Graziellah/Electronique-bagdeuse/pico/spi/spi_3.png

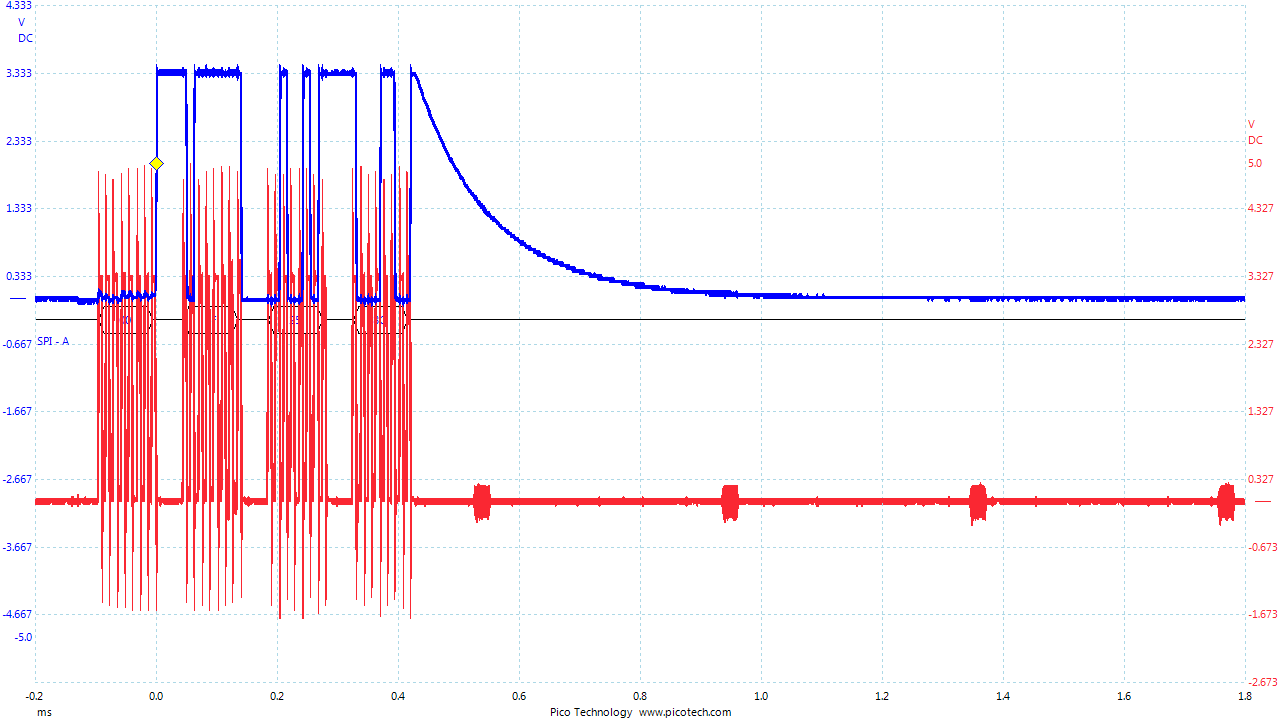
pico/spi/spi_3.png
