Graziellah/Electronique-bagdeuse/tps/42Electrons-TP02-REMAKE/TP02Remake/Project Outputs for TP02Remake/Job1.PDF

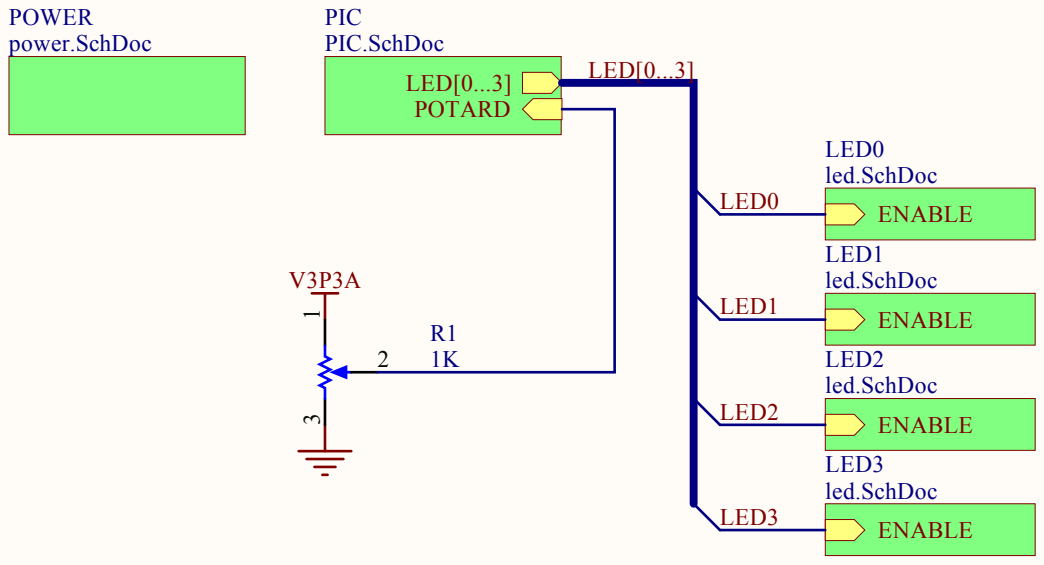
[picture p6: page 1]

Size: | N umber: | Rev
Date: / T ime: : 7 PM | | Sheet f *

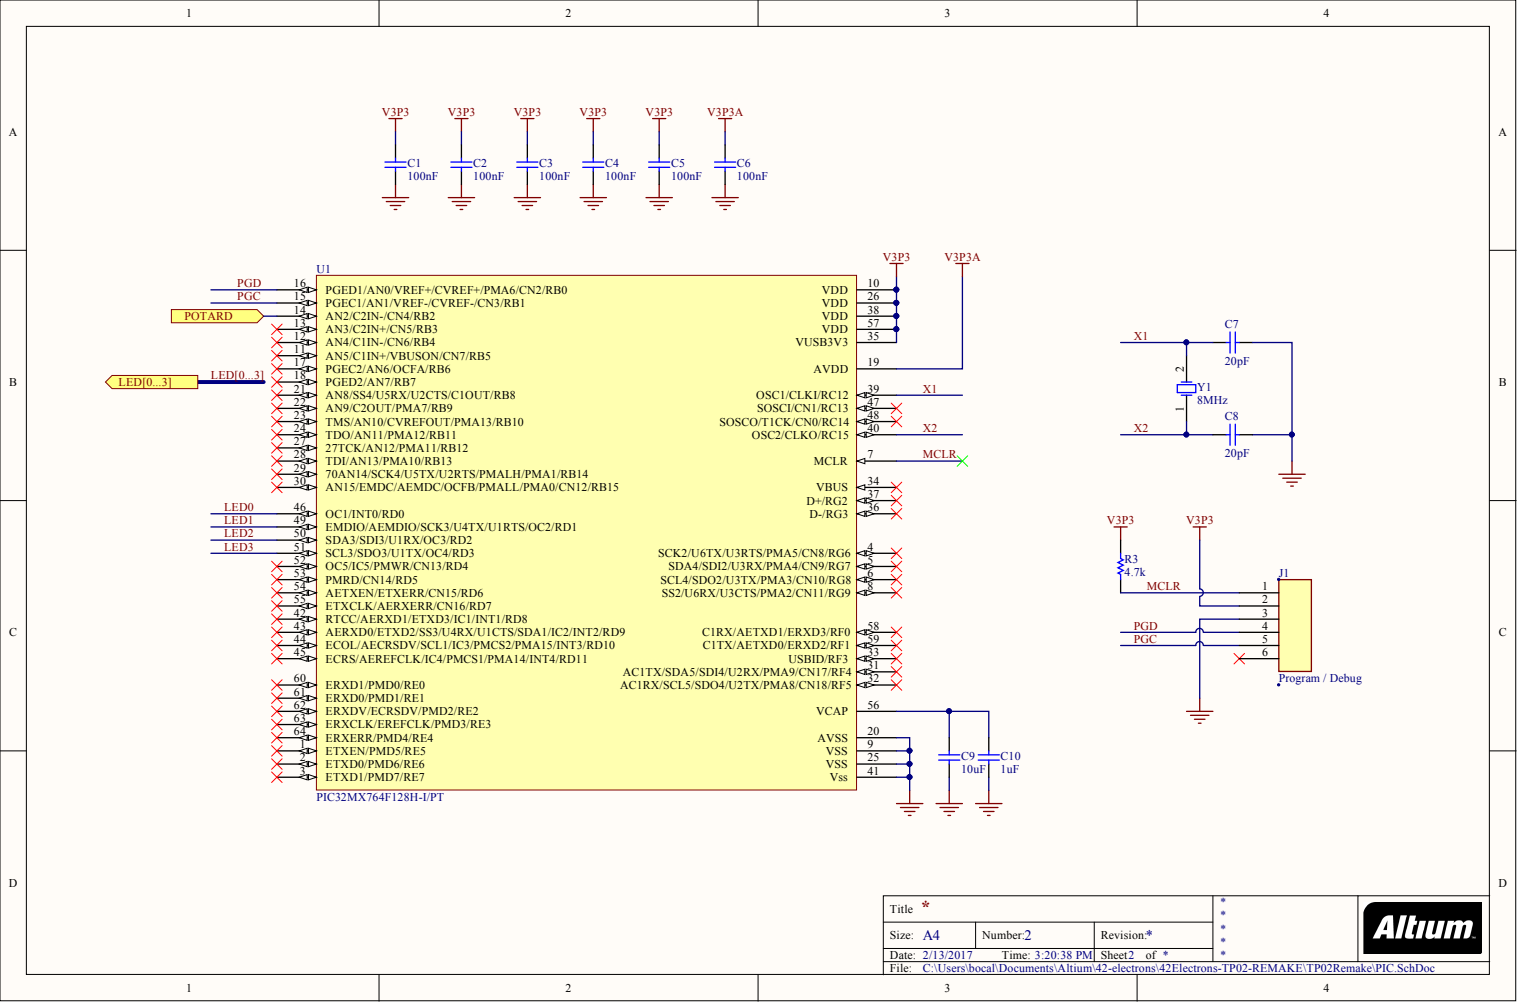
[picture p7: page 2]

2 0

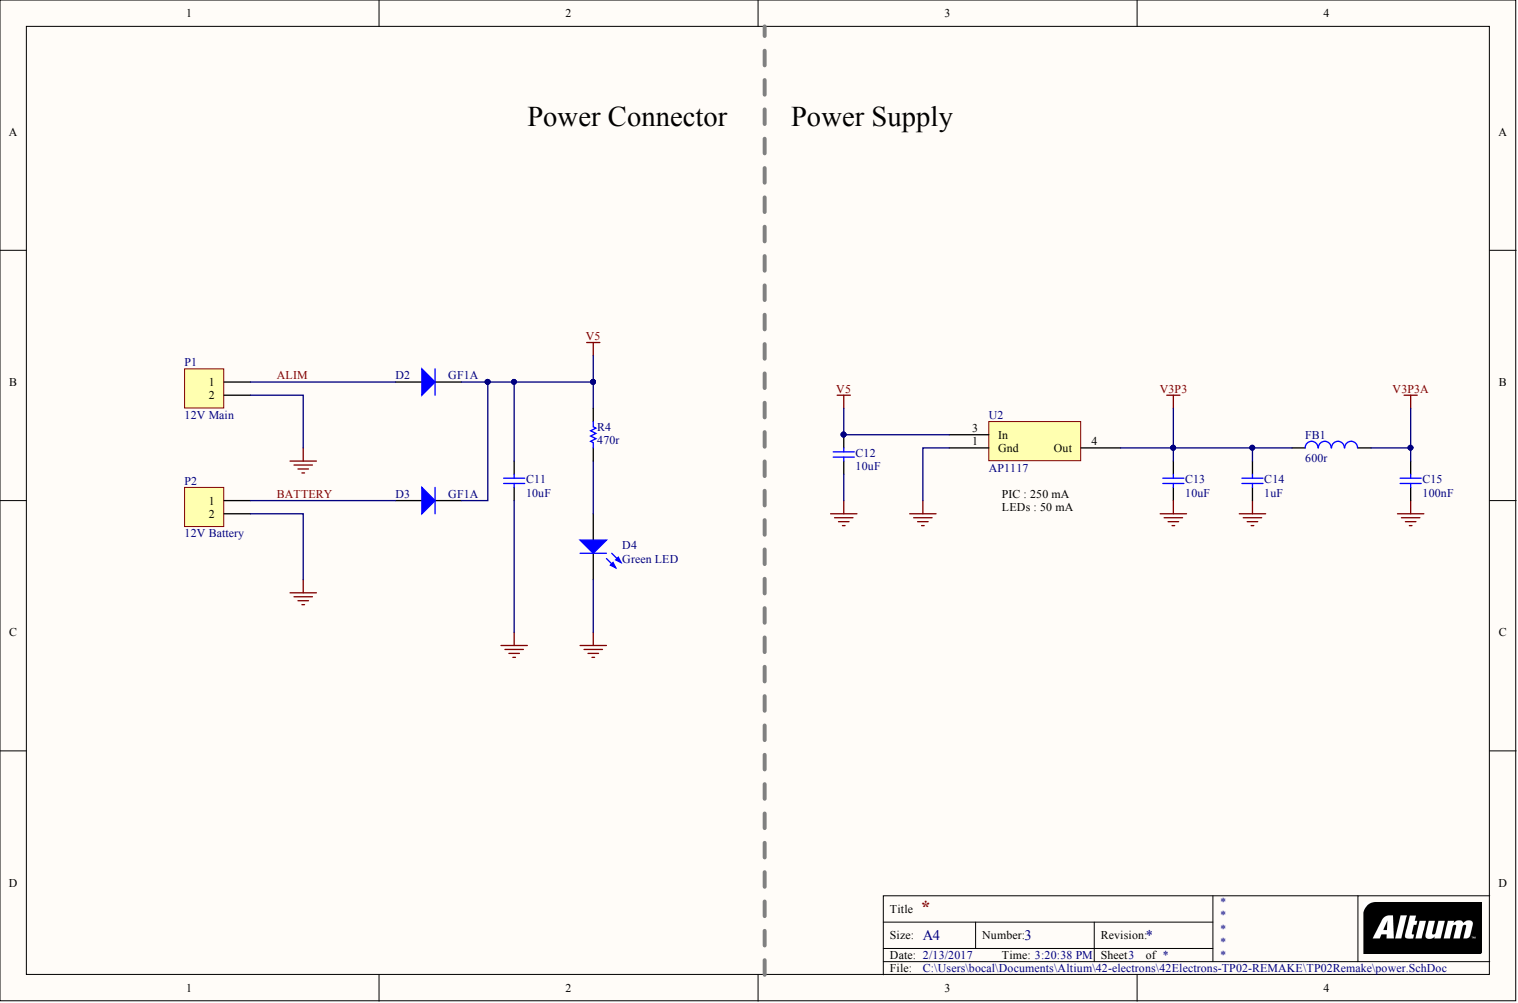
[picture p8: page 3]

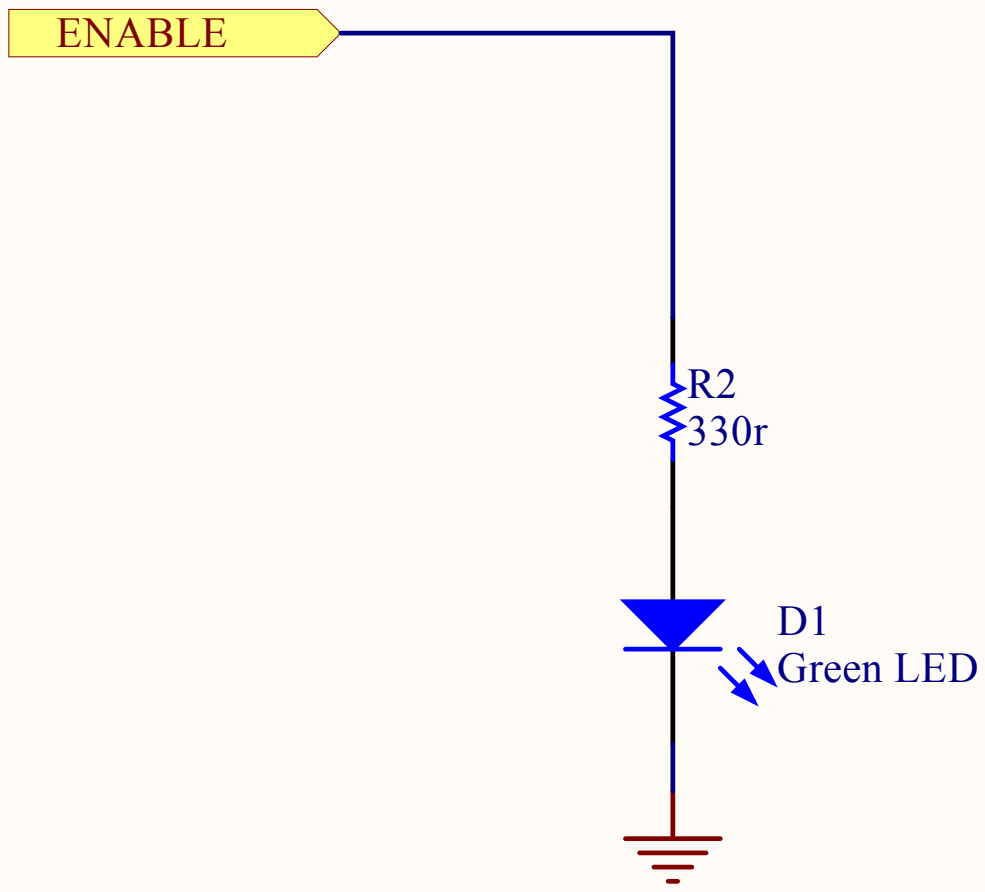
[picture p9: page 4]

Title * | * * *

Size: A4 | Number: 4 | Revision: *
2/13/2017 Time: 3:20:38 PM | | Sheet of *

C:\Users\bocal\Documents\Altium\42-electrons\42Electrons-TP02-REMAKE\TP02Remake\led.SchDoc
