Graziellah/Electronique-bagdeuse/tps/42Electrons-TP03/TP03/Project Outputs for TP02Remake/Assembly Drawings/Assembly Drawings.PDF

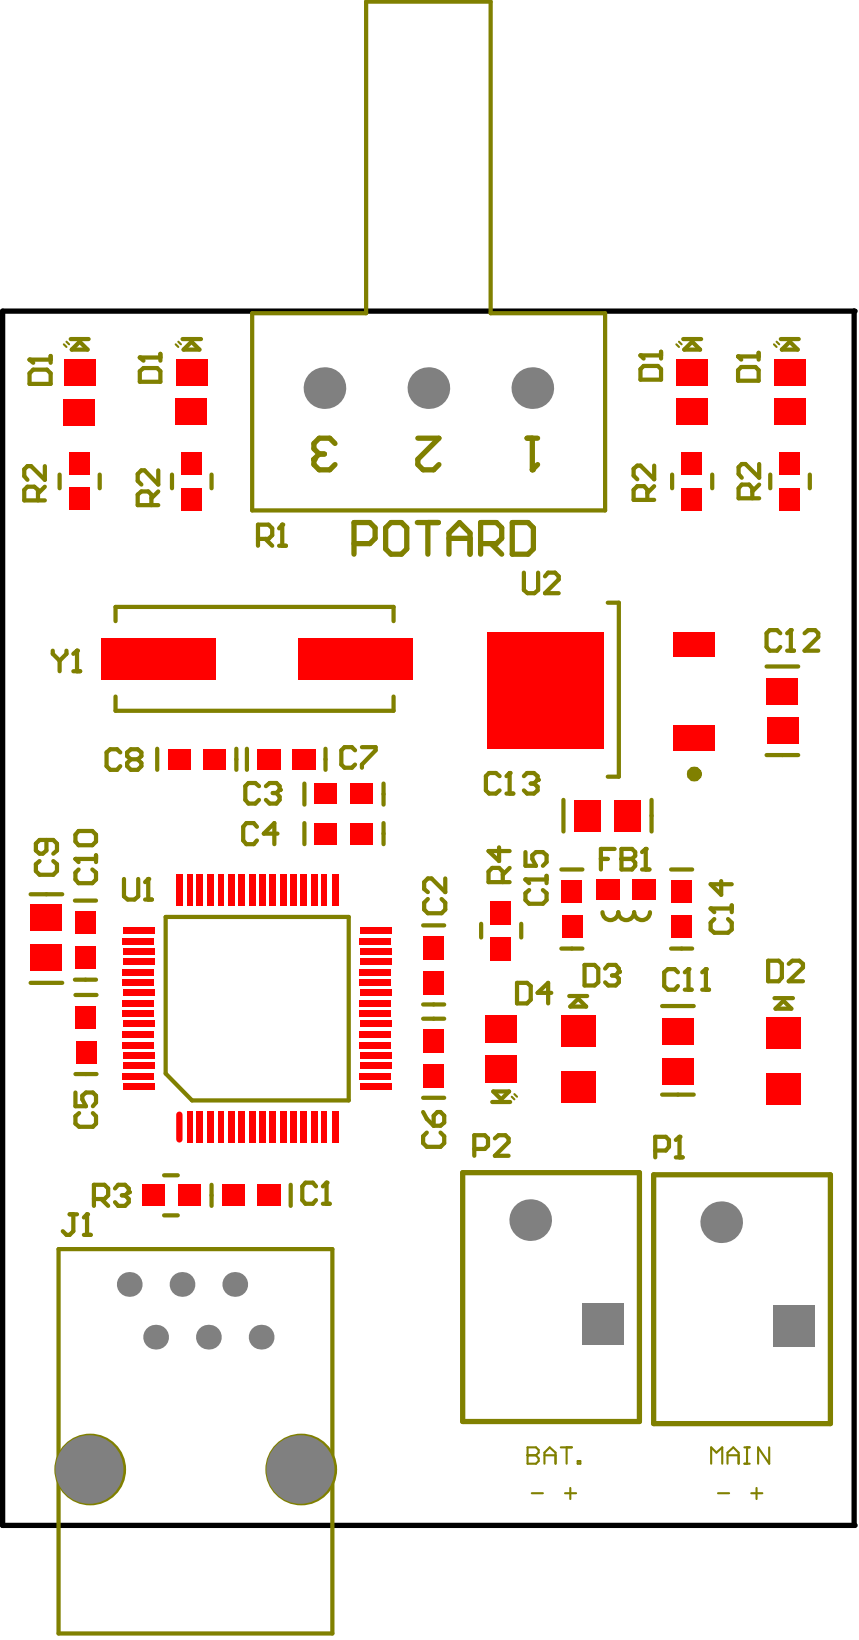
[picture p20: page 1]
