Graziellah/Electronique-bagdeuse/tps/42Electrons-TP03/TP03/Project Outputs for TP02Remake/Mechanical Drawings/Mechanical Drawings.PDF

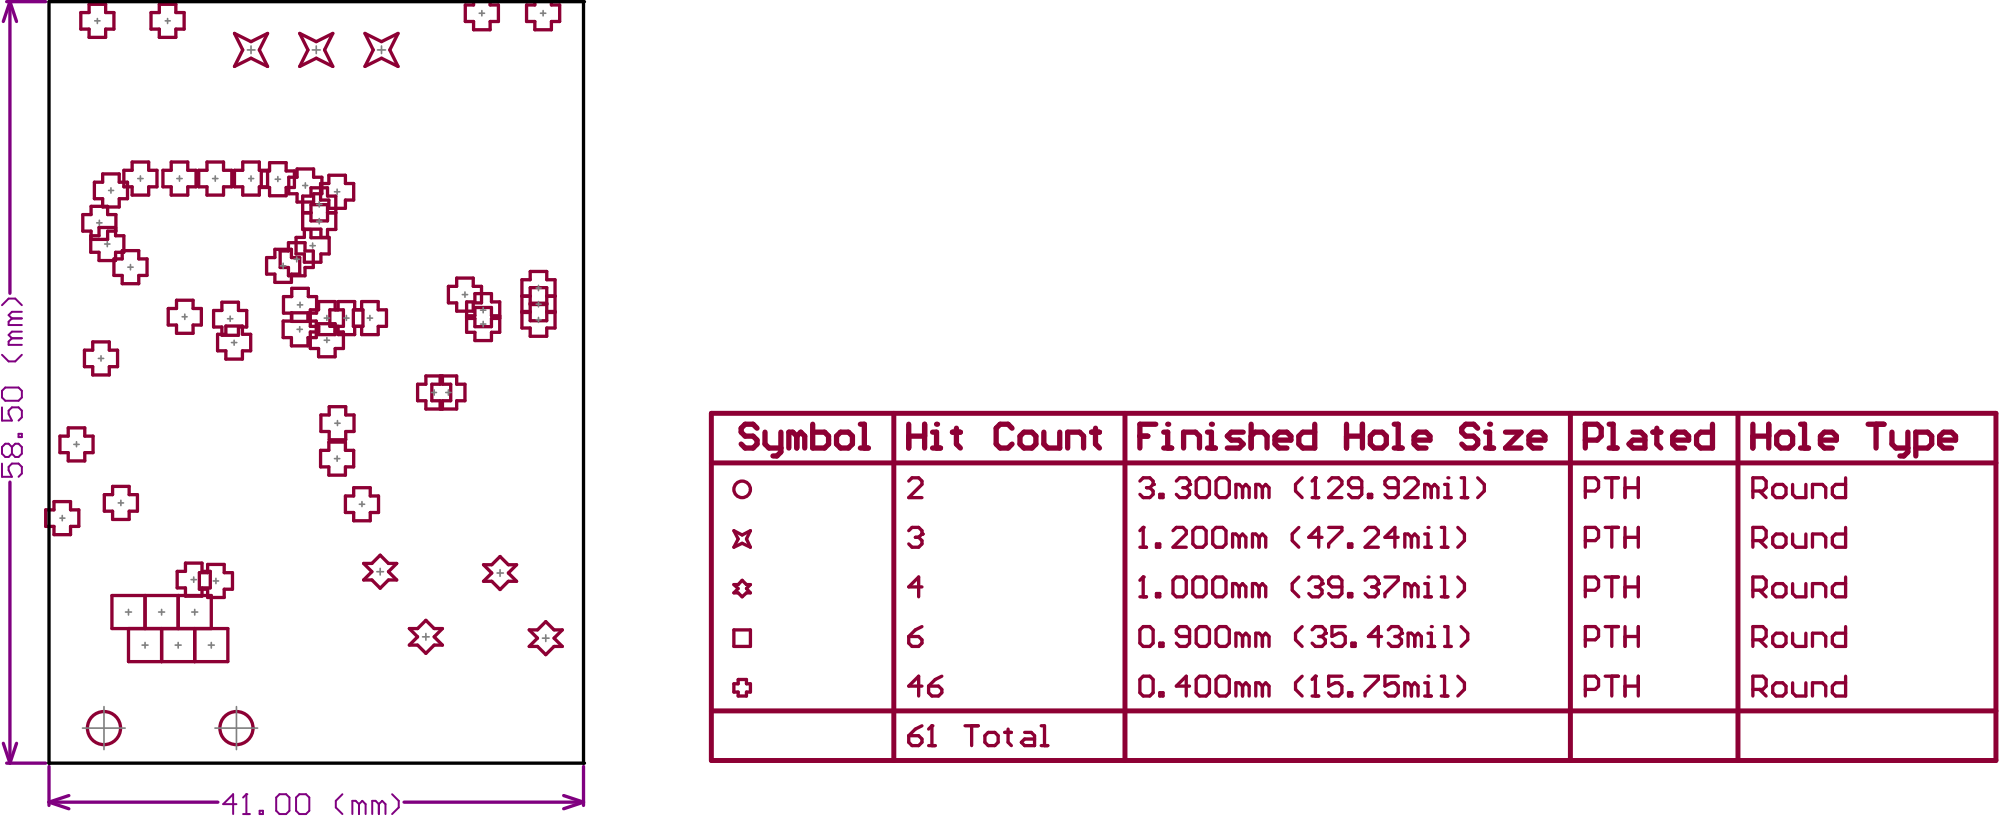
[picture p21: page 1]
