Graziellah/Electronique-bagdeuse/tps/42Electrons-TP03/TP03/Project Outputs for TP02Remake/Schematic Prints/Schematic Prints.PDF

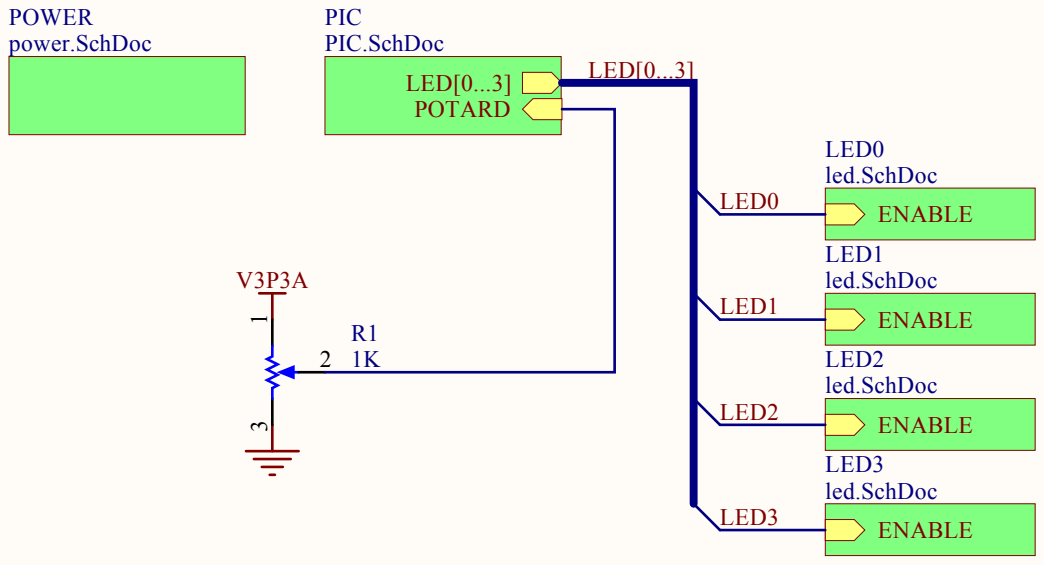
[picture p22: page 1]

Title * | * *

Size: A4 | Number: 1 | Revision: *
Date: 3/20/2017 Time: 1:25:23 PM | | Sheet of *

C:\Users\bocal\Documents\Altium\42-electrons\tps\42Electrons-TP03\TP03\TP2.SchDoc

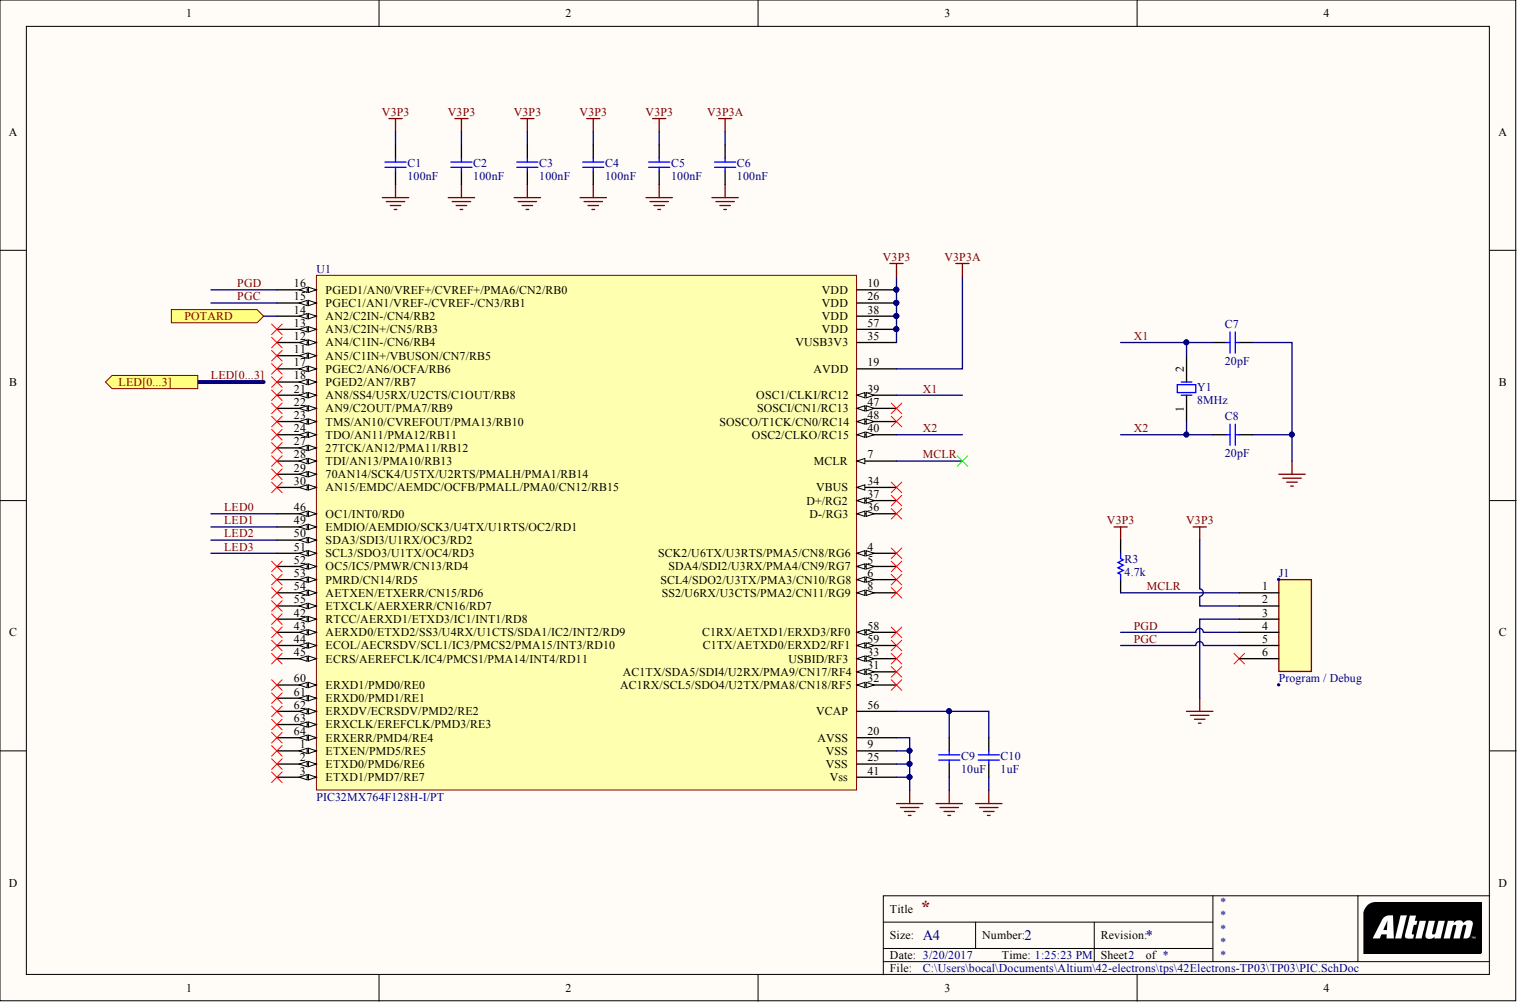
[picture p23: page 2]

2 0

Size: A | N umber: | Rev i s i o n :

/ / T ime: : : 3 PM | | Sheet o f

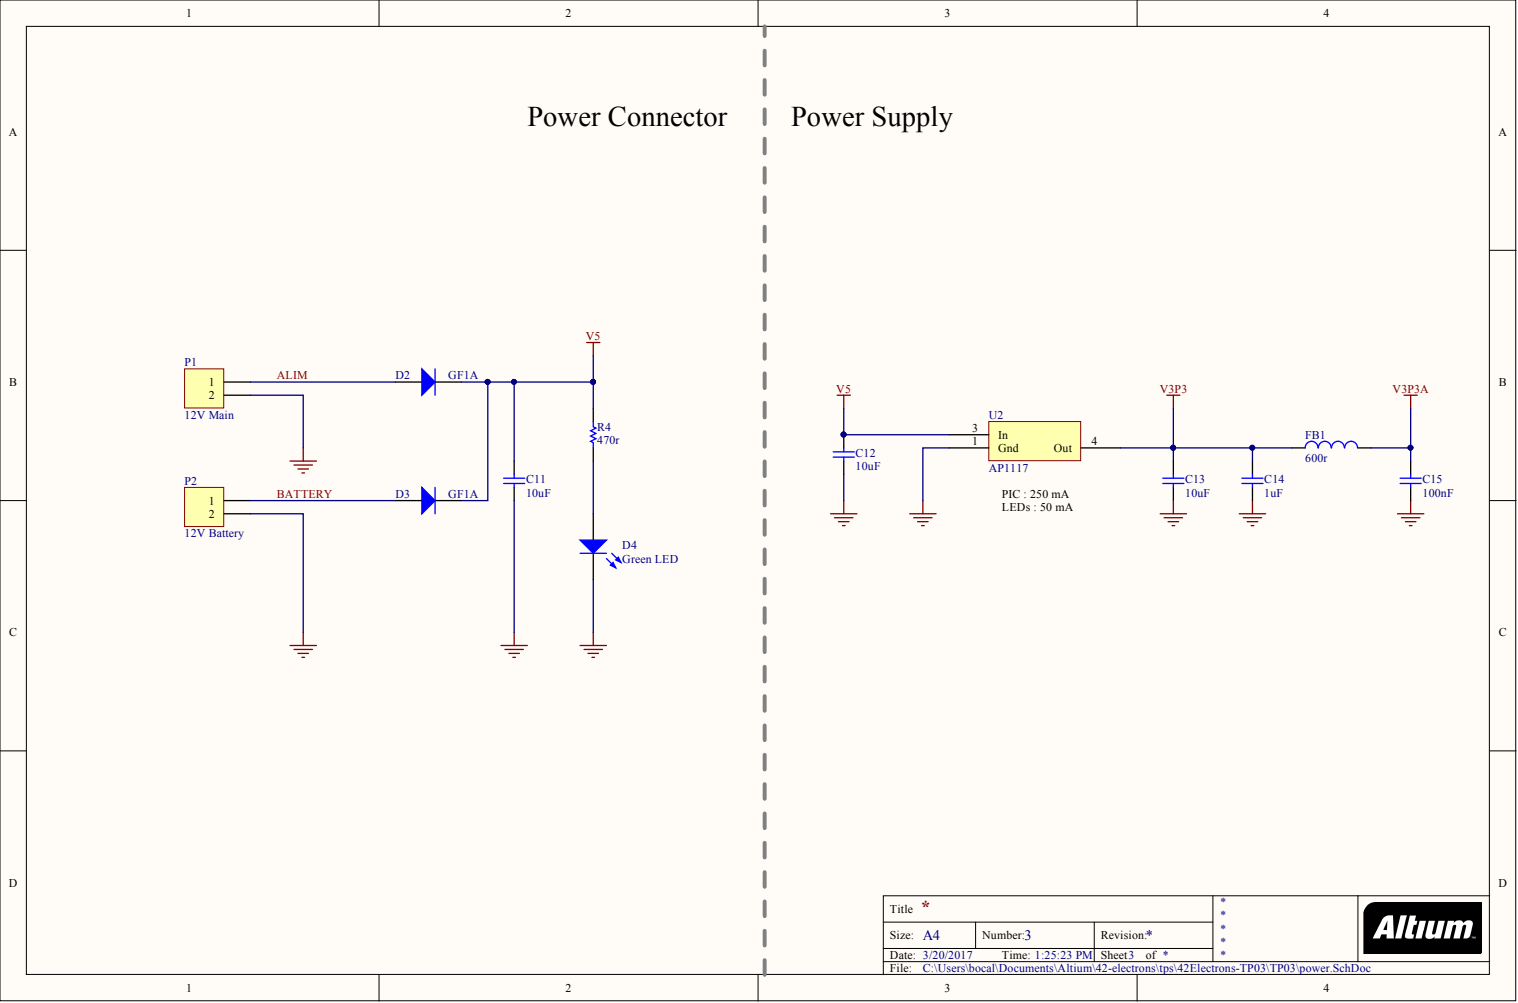
[picture p24: page 3]

Size: A | N umber: | Rev i s i o n :

/ / T ime: : : 3 PM | | Sheet o f

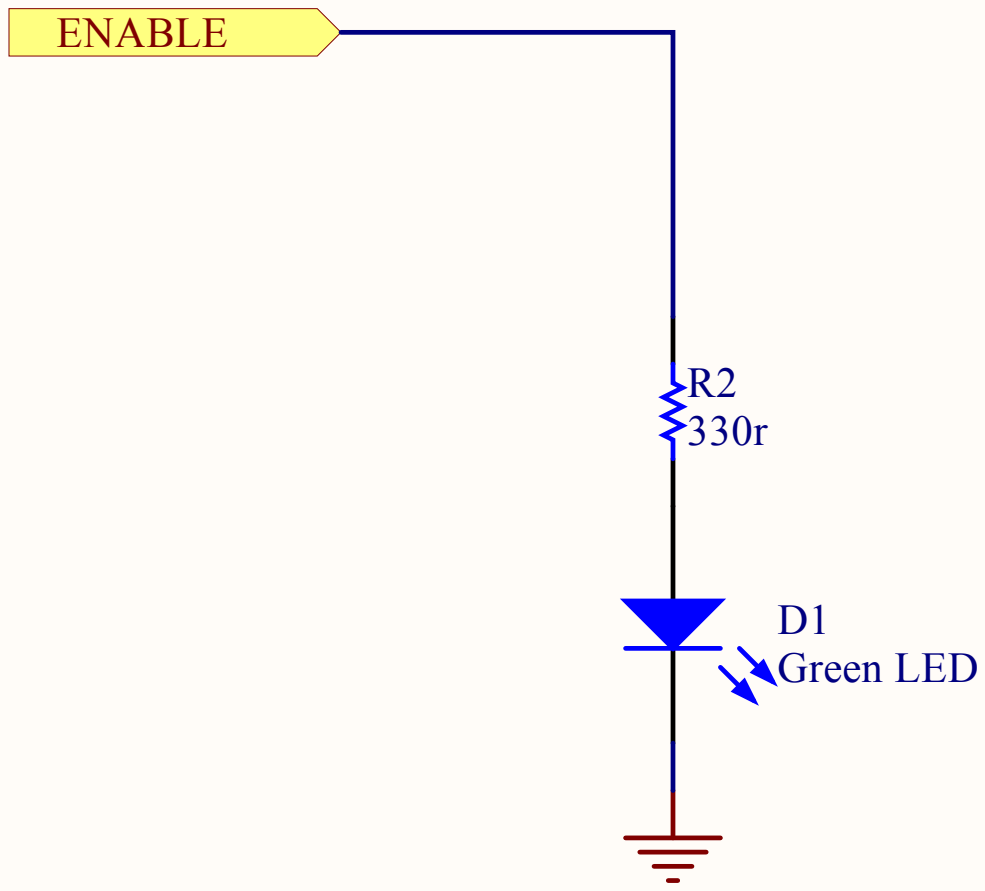
[picture p25: page 4]

Title * | * * *

Size: A4 | Number: 4 | Revision: *
3/20/2017 Time: 1:25:23 PM | | Sheet of *

C:\Users\bocal\Documents\Altium\42-electrons\tps\42Electrons-TP03\TP03\led.SchDoc
