Graziellah/Electronique-bagdeuse/tps/42Electrons-TP01-REMAKE/TP01Remake/Project Outputs for TP01Remake/Job1.PDF

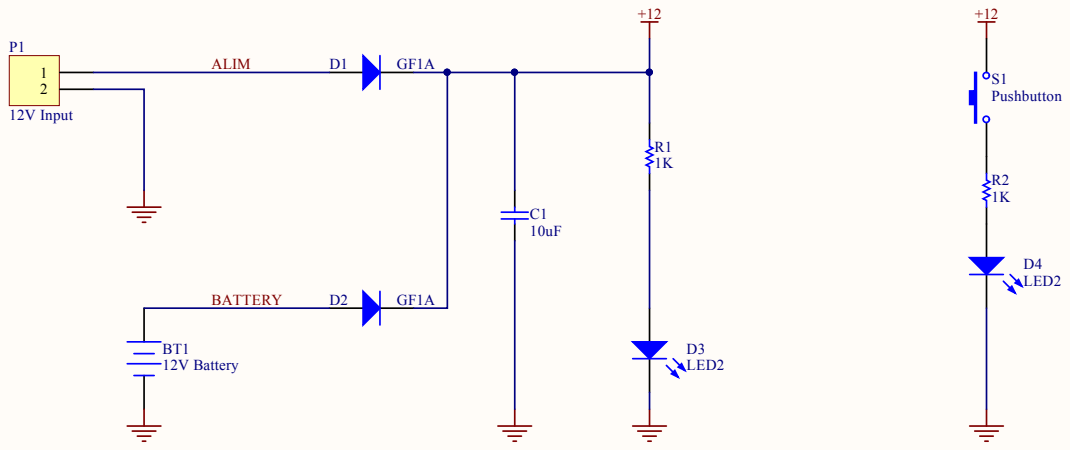
[picture p26: page 1]

Size: A 4 | N umber: 1 | Rev i s i o n : *
Date: 2 / 1 3 / 2 0 1 7 T ime: 2 : 5 6 : 0 6 PM | | Sheet * o f *
