Graziellah/Electronique-bagdeuse/tps/42Electrons-TP01-REMAKE/TP01Remake/Project Outputs for TP01Remake/Job2.PDF

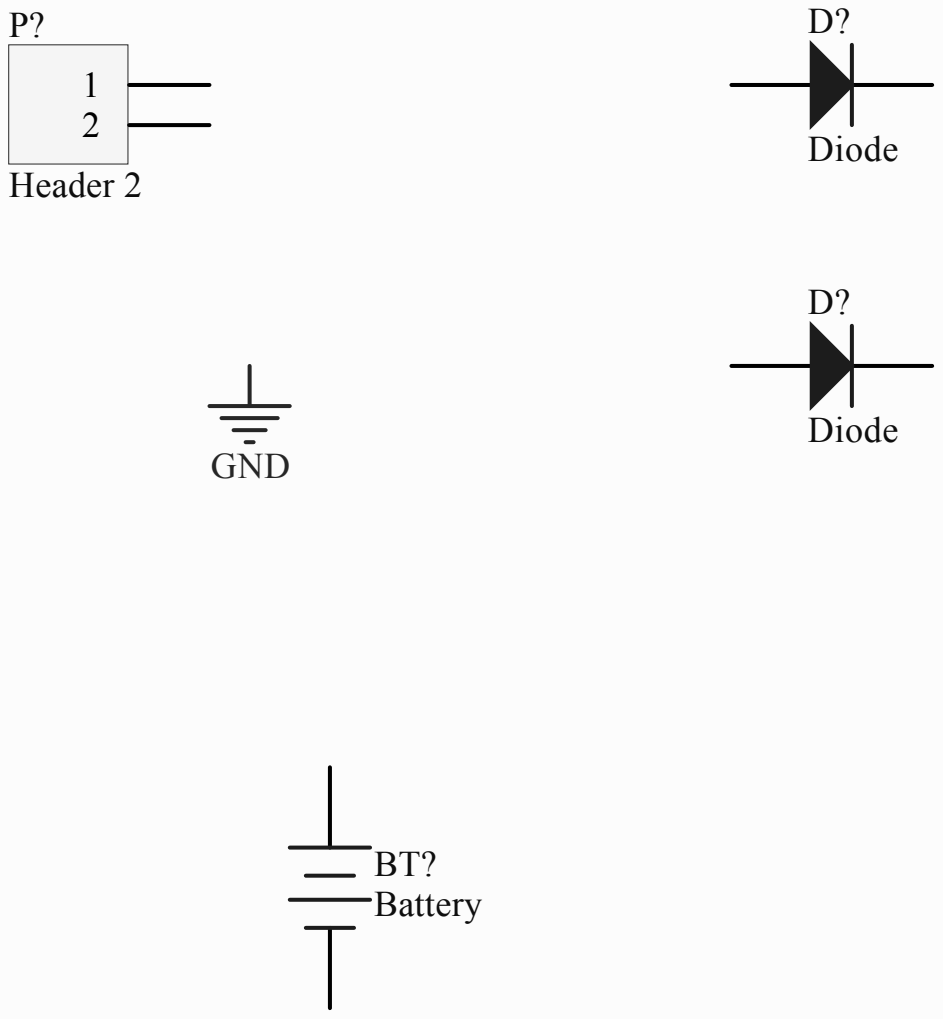
[picture p27: page 1]
